Turing-Dong/Constant-temperature-heating-table/project_v1.2/program_v1.2/Drivers/SYSTEM/sys/sys.h

/**
 ****************************************************************************************************
 * @file        sys.h
 * @author      正点原子团队(ALIENTEK)
 * @version     V1.0
 * @date        2023-08-01
 * @brief       系统初始化代码(包括时钟配置/中断管理/GPIO设置等)
 * @license     Copyright (c) 2020-2032, 广州市星翼电子科技有限公司
 ****************************************************************************************************
 * @attention
 *
 * 实验平台:正点原子 M48Z-M3最小系统板STM32F103版
 * 在线视频:www.yuanzige.com
 * 技术论坛:www.openedv.com
 * 公司网址:www.alientek.com
 * 购买地址:openedv.taobao.com
 *
 ****************************************************************************************************
 */

#ifndef __SYS_H
#define __SYS_H

#include "stm32f1xx.h"


/**
 * SYS_SUPPORT_OS用于定义系统文件夹是否支持OS
 * 0,不支持OS
 * 1,支持OS
 */
#define SYS_SUPPORT_OS          0
typedef uint8_t u8;
typedef uint16_t u16;
typedef uint32_t u32;


/*函数申明*******************************************************************************************/

void sys_nvic_set_vector_table(uint32_t baseaddr, uint32_t offset);             /* 设置中断偏移量 */
void sys_standby(void);                                                         /* 进入待机模式 */
void sys_soft_reset(void);                                                      /* 系统软复位 */
uint8_t sys_clock_set(uint32_t plln);                                           /* 时钟设置函数 */
void sys_stm32_clock_init(uint32_t plln);                                       /* 系统时钟初始化函数 */

/* 以下为汇编函数 */
void sys_wfi_set(void);                                                         /* 执行WFI指令 */
void sys_intx_disable(void);                                                    /* 关闭所有中断 */
void sys_intx_enable(void);                                                     /* 开启所有中断 */
void sys_msr_msp(uint32_t addr);                                                /* 设置栈顶地址 */

#endif
